owenmcgrath/home-automation/Thermostat/Code/dht22test.py

import Adafruit_DHT

DHT_SENSOR = Adafruit_DHT.DHT22

DHT_PIN = 22

while True:
	humidity, temperature = Adafruit_DHT.read_retry(DHT_SENSOR, DHT_PIN)
	if humidity is not None and temperature is not None:
		print("Temp={0:0.1f}*C Humidity={1:0.1f}%".format(temperature, humidity))
	else :
		print("Failed to retrieve data from humidity sensor")
