owenmcgrath/home-automation/Thermostat/Code/blinkatest.py

import board
import digitalio
import busio

pin = digitalio.DigitalInOut(board.D4)
print("Digital IO ok")

i2c = busio.I2C(board.SCL, board.SDA)
print("I2C Ok")

spi = busio.SPI(board.SCLK, board.MOSI, board.MISO)
print("SPI Ok")

print("done")
